dimitarminchev/HAS8266/2018/Hardware/HAS.sch

## EAGLE design 2018/Hardware/HAS.sch (2018-06-07)

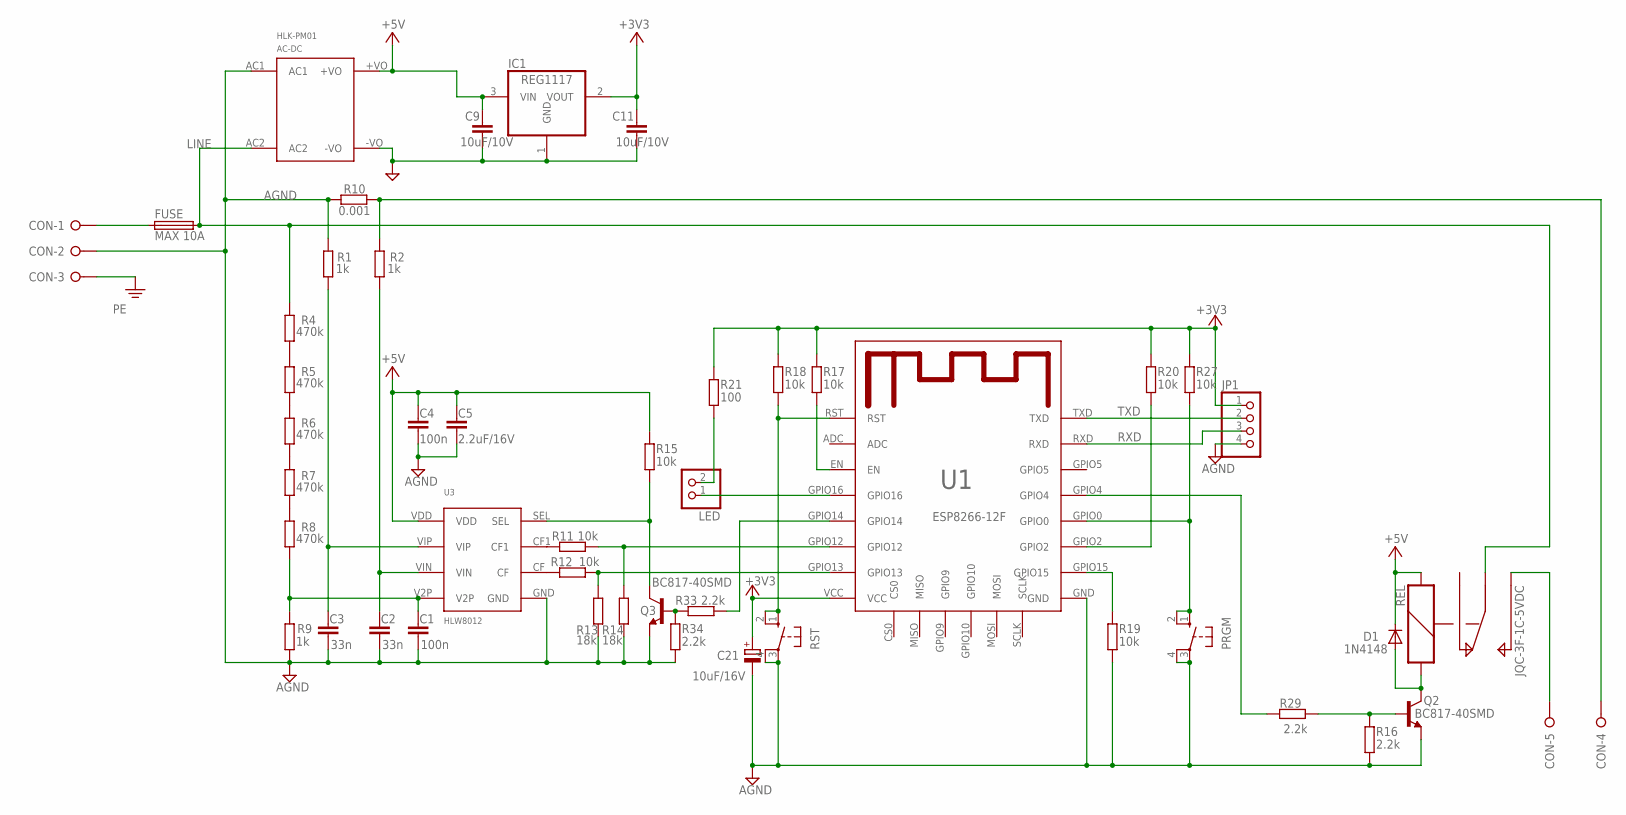
[picture p25: schematic HAS.sch]

Parts:
AC-DC: HLK-PM01
C1, C4: 100n; C0805
C2, C3: 33n; C0805
C5: 2.2uF/16V; C0805
C9, C11: 10uF/10V; C1206
C21: 10uF/16V; SMC_B
CON: W237-05P; W237-5P
D1: 1N4148; SOD123
FUSE: MAX 10A; SH22
IC1: REG1117; SOT223
JP1: PINHD-1X4; 1X04
LED: PINHD-1X2; 1X02
PRGM: 10-XX; B3F-10XX
Q2, Q3: BC817-40SMD; SOT23-BEC
R1, R2, R9: 1k; R0805
R4, R5, R6, R7, R8: 470k; R0805
R10: 0.001; R2512
R11, R12, R15, R17, R18, R19, R20, R27: 10k; R0805
R13, R14: 18k; R0805
R16, R29, R33, R34: 2.2k; R0805
R21: 100; R0805
REL: JQC-3F-1C-5VDC
RST: 10-XX; B3F-10XX
U1: ESP8266-12F
U3: HLW8012

Connections:
+3V3: C11.2, C21.+, IC1.2 (VOUT), JP1.1, R17.1, R18.1, R20.1, R21.1, R27.1, U1.VCC
+5V: AC-DC.+VO, C4.1, C5.1, C9.2, D1.C, IC1.3 (VIN), R15.1, REL.R2, U3.VDD
AGND: AC-DC.-VO, AC-DC.AC1, C1.2, C2.2, C3.2, C4.2, C5.2, C9.1, C11.1, C21.-, CON.2, IC1.1 (GND), JP1.4, PRGM.3, PRGM.4 (P1), Q2.E, Q3.E, R1.1, R9.1, R10.1, R13.2, R14.2, R16.2, R19.2, R34.2, RST.3, RST.4 (P1), U1.GND, U3.GND
LINE: AC-DC.AC2, FUSE.2, R4.2, REL.COM
N: CON.4, R2.1, R10.2
unnamed: C1.1, R8.1, R9.2, U3.V2P
unnamed: R6.1, R7.2
unnamed: Q3.C, R15.2, U3.SEL
unnamed: R11.1, U3.CF1
unnamed: R12.1, U3.CF
unnamed: C2.1, R2.2, U3.VIN
unnamed: C3.1, R1.2, U3.VIP
unnamed: R7.1, R8.2
unnamed: R5.1, R6.2
unnamed: R4.1, R5.2
unnamed: LED.1, U1.GPIO16
unnamed: R11.2, R14.1, U1.GPIO12
unnamed: R12.2, R13.1, U1.GPIO13
unnamed: R29.1, U1.GPIO4
unnamed: Q2.B, R16.1, R29.2
unnamed: PRGM.1 (S), PRGM.2 (S1), R27.2, U1.GPIO0
unnamed: Q3.B, R33.2, R34.1
unnamed: CON.5, REL.NO
unnamed: R17.2, U1.EN
unnamed: LED.2, R21.2
unnamed: R18.2, RST.1 (S), RST.2 (S1), U1.RST
unnamed: CON.1, FUSE.1
unnamed: R20.2, U1.GPIO2
unnamed: R33.1, U1.GPIO14
unnamed: D1.A, Q2.C, REL.R1
unnamed: R19.1, U1.GPIO15
PE: CON.3
RXD: JP1.3, U1.RXD
TXD: JP1.2, U1.TXD
