dimitarminchev/HAS8266/2020/LAS8266/HLW8012.h

/*
HLW8012 1.0.0
---
Copyright (C) 2016 by Xose Perez <xose.perez@gmail.com>

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
You should have received a copy of the GNU General Public License
along with this program.  If not, see <http://www.gnu.org/licenses/>.
*/

#ifndef _HLW_8012_h
#define _HLW_8012_h

// Internal voltage reference value
#define V_REF 2.43

// The factor of a 1mOhm resistor
// as per recomended circuit in datasheet
// A 1mOhm resistor allows a ~30A max measurement
#define R_CURRENT 0.001 // 0.001

// This is the factor of a voltage divider of 6x 470K upstream and 1k downstream
// as per recomended circuit in datasheet
#define R_VOLTAGE 2281

// Frequency of the HLW8012 internal clock
#define F_OSC 3249888 // 3579000

// Minimum delay between selecting a mode and reading a sample
#define READING_INTERVAL 1000

// Maximum pulse with in microseconds
// If longer than this pulse width is reset to 0
// This value is purely experimental.
// Higher values allow for a better precission but reduce sampling rate
// and response speed to change
// Lower values increase sampling rate but reduce precission
// Values below 0.5s are not recommended since current and voltage output
// will have no time to stabilise
#define PULSE_TIMEOUT 1000000

// CF1 mode
typedef enum {
    MODE_CURRENT,
    MODE_VOLTAGE
} hlw8012_mode_t;

class HLW8012
{

  public:
    void cf_interrupt();
    void cf1_interrupt();

    void begin(
        unsigned char cf_pin,
        unsigned char cf1_pin,
        unsigned char sel_pin,
        unsigned char currentWhen = HIGH,
        bool use_interrupts = true,
        unsigned long pulse_timeout = PULSE_TIMEOUT);

    void setMode(hlw8012_mode_t mode);
    hlw8012_mode_t getMode();
    hlw8012_mode_t toggleMode();

    String getInfo(); // TODO

    double getCurrent();
    unsigned int getVoltage();
    unsigned int getActivePower();
    unsigned int getApparentPower();
    double getPowerFactor();
    unsigned int getReactivePower();
    unsigned long getEnergy(); // in Ws
    void resetEnergy();

    void setResistors(double current, double voltage_upstream, double voltage_downstream);

    void expectedCurrent(double current);
    void expectedVoltage(unsigned int current);
    void expectedActivePower(unsigned int power);

    double getCurrentMultiplier() { return _current_multiplier; };
    double getVoltageMultiplier() { return _voltage_multiplier; };
    double getPowerMultiplier() { return _power_multiplier; };

    void setCurrentMultiplier(double current_multiplier) { _current_multiplier = current_multiplier; };
    void setVoltageMultiplier(double voltage_multiplier) { _voltage_multiplier = voltage_multiplier; };
    void setPowerMultiplier(double power_multiplier) { _power_multiplier = power_multiplier; };
    void resetMultipliers();

  private:
    unsigned char _cf_pin;
    unsigned char _cf1_pin;
    unsigned char _sel_pin;

    double _current_resistor = R_CURRENT;
    double _voltage_resistor = R_VOLTAGE;

    double _current_multiplier; // Unit: us/A
    double _voltage_multiplier; // Unit: us/V
    double _power_multiplier;   // Unit: us/W

    unsigned long _pulse_timeout = PULSE_TIMEOUT;    // Unit: us
    volatile unsigned long _voltage_pulse_width = 0; // Unit: us
    volatile unsigned long _current_pulse_width = 0; // Unit: us
    volatile unsigned long _power_pulse_width = 0;   // Unit: us
    volatile unsigned long _pulse_count = 0;

    double _current = 0;
    unsigned int _voltage = 0;
    unsigned int _power = 0;

    unsigned char _current_mode = HIGH;
    volatile unsigned char _mode;

    bool _use_interrupts = true;
    volatile unsigned long _last_cf_interrupt = 0;
    volatile unsigned long _last_cf1_interrupt = 0;
    volatile unsigned long _first_cf1_interrupt = 0;

    void _checkCFSignal();
    void _checkCF1Signal();
    void _calculateDefaultMultipliers();
};

#endif
